jassuncao/smart-fan-controller/simulation/triac_experiments.asc

C1: cap; 440µ
C2: cap; 1µ
C3: cap; 220n
D1: zener; BZX84C6V2L
D2: diode; 1N4148
D3: diode; 1N4148
D4: diode; 1N4148
R1: res; 3000
R2: res; 120
R3: res; 220
R4: res; 1000k
U1: TRIAC; L601E3
V1: voltage; SINE(0 310 50)
Named nets: 0
.inc Z:\\hd\\Work\\Electronics\\tectriac.lib
.tran 0.2
