jassuncao/smart-fan-controller/simulation/CapacitiveHalfWaveSimulation.asc

BlockingDiode: diode; ES1D
C1: cap; 470n
C2: cap; 22µ
C3: cap; 470n
D1: diode; 1N4148
D2: diode; 1N4148
OutputCapacitance: cap; 470µ
R1: res; 120
R2: res; 560K
R3: res; 560K
R4: res; 1000k
R5: res; 200K
R6: res; 1000k
R_Load_regulated: res; 1000
R_Load_unregulated: res; 1000
U1: LT1086-3.3
Vin: voltage; SINE(0 310 50 0)
ZenerDiode1: zener; BZX84C6V2L
ZenerDiode: zener; BZX84C6V2L
Named nets: 0
.tran 2
Capacitive Half-Wave Rectification (with Blocking Diode Post-Zener)
Optional LDO for output regulation
220Vrms, 50Hz
Simulate: transient analysis, 2 seconds
Transformerless Power Supply
