jassuncao/smart-fan-controller/simulation/power_supply.asc

C1: cap; 0.47µ; V=400
C2: cap; 470µ; V=16
D1: zener; BZX84C5V6
D2: diode; 1N4148
R1: res; 1K
R2: res; 470
R3: res; 800
V1: voltage; SINE(0 311 50); AC 220
Named nets: 0
.include BZX84C5V6.inc
.tran 1
